andrewfernie/CADDeck/data/ButtonLayout10.png

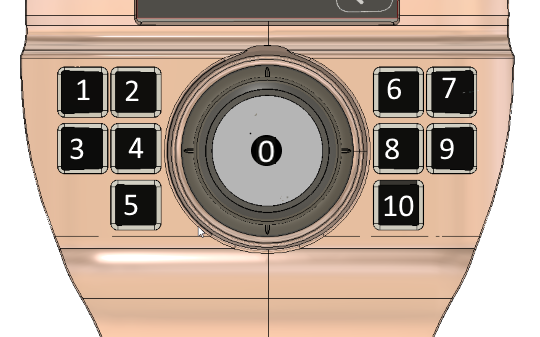
data/ButtonLayout10.png
