andrewfernie/CADDeck/data/ButtonLayout.png

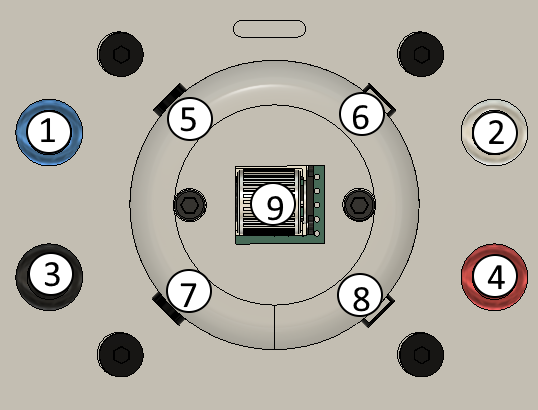
data/ButtonLayout.png
