andrewfernie/CADDeck/images/cadapp.png

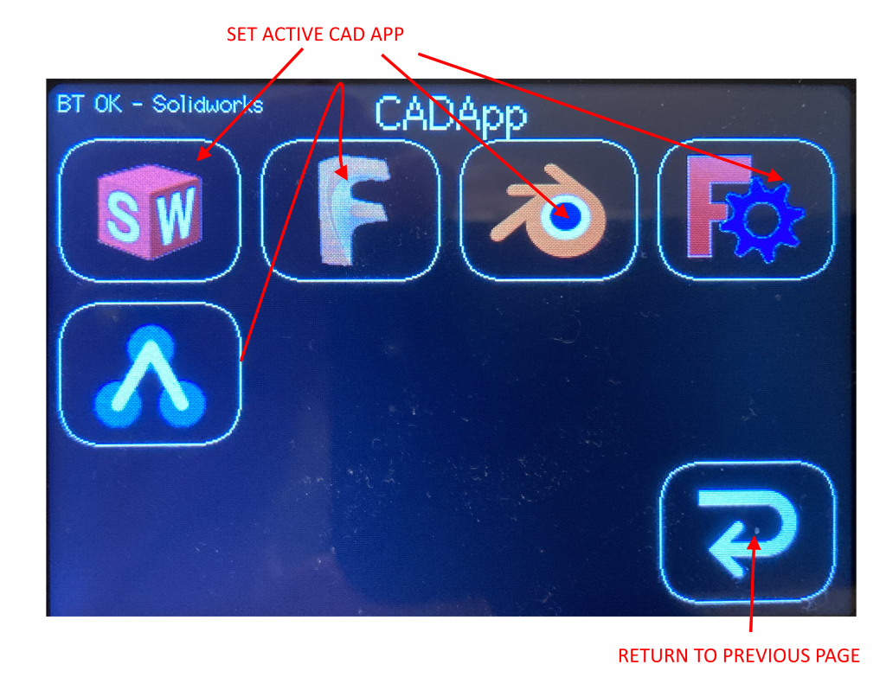
images/cadapp.png
