andrewfernie/CADDeck/images/Case.png

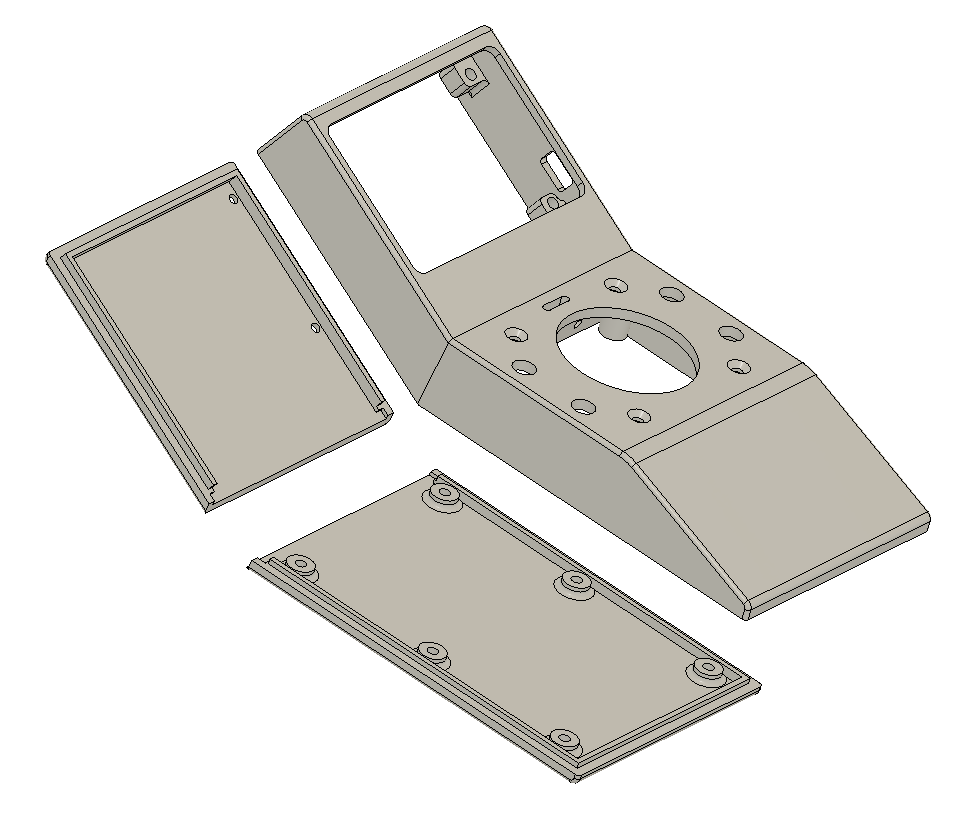
images/Case.png
