andrewfernie/CADDeck/images/ConfigurePan.png

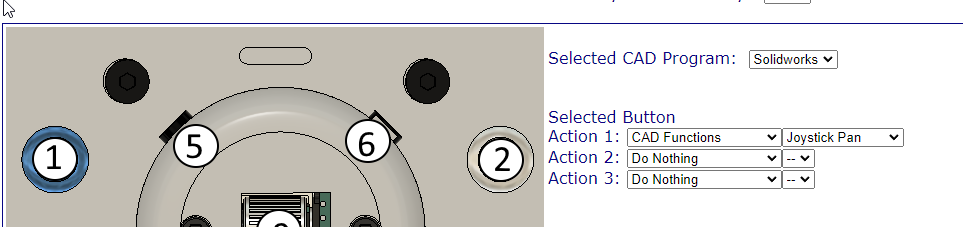
images/ConfigurePan.png
