andrewfernie/CADDeck/images/pcb.png

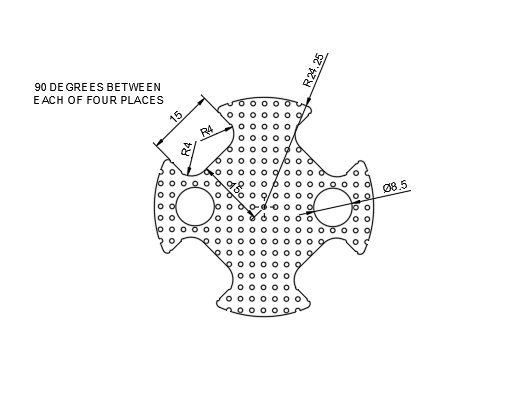
images/pcb.png
