andrewfernie/CADDeck/images/Assembly.png

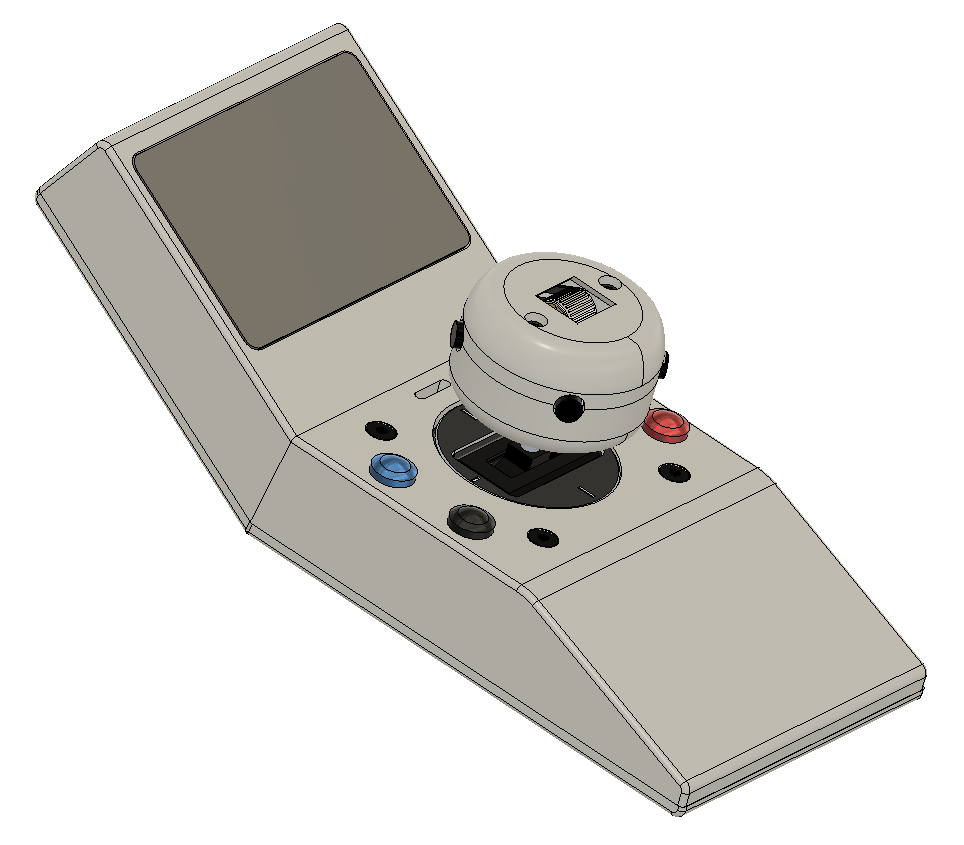
images/Assembly.png
