andrewfernie/CADDeck/hardware/Electrical/CADDeck.kicad_pcb

## KiCad design schematics/Microbee_Kit_Core_Board/rom_bank.kicad_sch

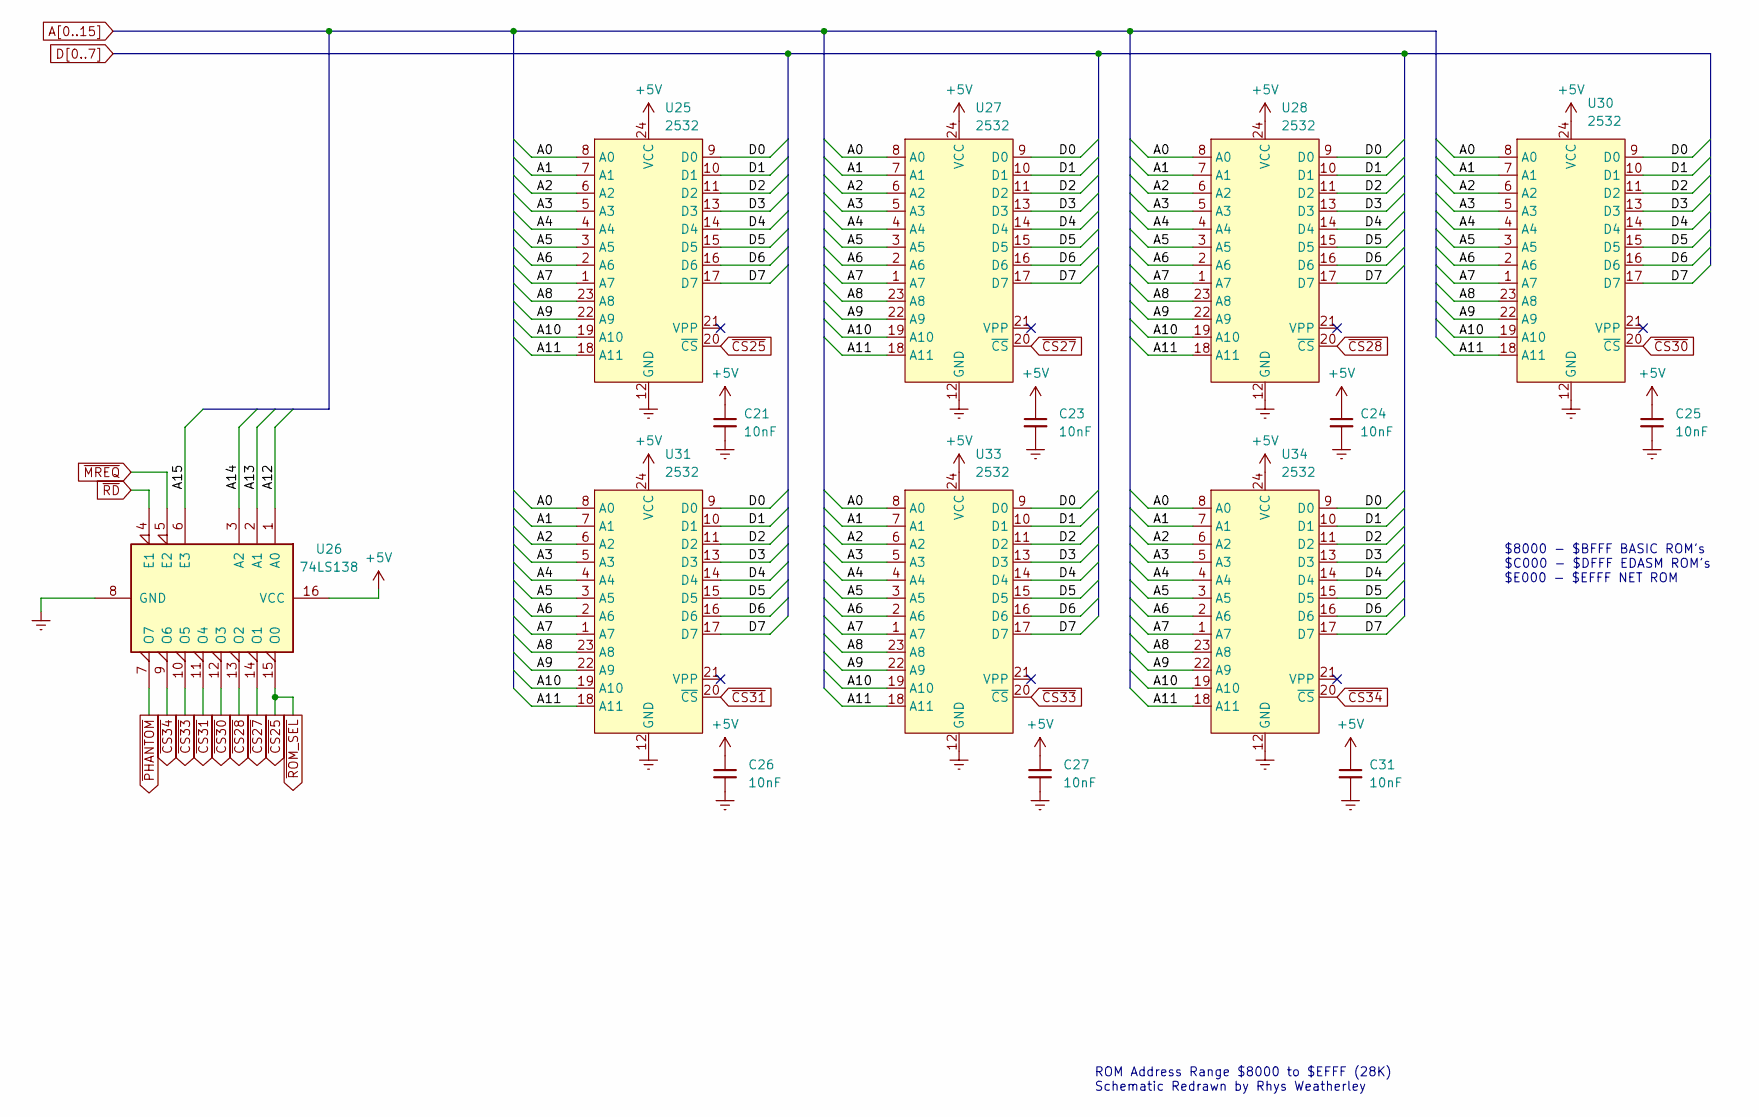
[picture p36: schematic rom_bank.kicad_sch]

Parts:
C21, C23, C24, C25, C26, C27, C31: 10nF
U25, U27, U28, U30, U31, U33, U34: 2532; DIP-24_W15.24mm
U26: 74LS138

Connections:
+5V: C21.1, C23.1, C24.1, C25.1, C26.1, C27.1, C31.1, U25.24 (VCC), U26.16 (VCC), U27.24 (VCC), U28.24 (VCC), U30.24 (VCC), U31.24 (VCC), U33.24 (VCC), U34.24 (VCC)
A0: U25.8 (A0), U27.8 (A0), U28.8 (A0), U30.8 (A0), U31.8 (A0), U33.8 (A0), U34.8 (A0)
A1: U25.7 (A1), U27.7 (A1), U28.7 (A1), U30.7 (A1), U31.7 (A1), U33.7 (A1), U34.7 (A1)
A2: U25.6 (A2), U27.6 (A2), U28.6 (A2), U30.6 (A2), U31.6 (A2), U33.6 (A2), U34.6 (A2)
A3: U25.5 (A3), U27.5 (A3), U28.5 (A3), U30.5 (A3), U31.5 (A3), U33.5 (A3), U34.5 (A3)
A4: U25.4 (A4), U27.4 (A4), U28.4 (A4), U30.4 (A4), U31.4 (A4), U33.4 (A4), U34.4 (A4)
A5: U25.3 (A5), U27.3 (A5), U28.3 (A5), U30.3 (A5), U31.3 (A5), U33.3 (A5), U34.3 (A5)
A6: U25.2 (A6), U27.2 (A6), U28.2 (A6), U30.2 (A6), U31.2 (A6), U33.2 (A6), U34.2 (A6)
A7: U25.1 (A7), U27.1 (A7), U28.1 (A7), U30.1 (A7), U31.1 (A7), U33.1 (A7), U34.1 (A7)
A8: U25.23 (A8), U27.23 (A8), U28.23 (A8), U30.23 (A8), U31.23 (A8), U33.23 (A8), U34.23 (A8)
A9: U25.22 (A9), U27.22 (A9), U28.22 (A9), U30.22 (A9), U31.22 (A9), U33.22 (A9), U34.22 (A9)
A10: U25.19 (A10), U27.19 (A10), U28.19 (A10), U30.19 (A10), U31.19 (A10), U33.19 (A10), U34.19 (A10)
A11: U25.18 (A11), U27.18 (A11), U28.18 (A11), U30.18 (A11), U31.18 (A11), U33.18 (A11), U34.18 (A11)
A12: U26.1 (A0)
A13: U26.2 (A1)
A14: U26.3 (A2)
A15: U26.6 (E3)
D0: U25.9 (D0), U27.9 (D0), U28.9 (D0), U30.9 (D0), U31.9 (D0), U33.9 (D0), U34.9 (D0)
D1: U25.10 (D1), U27.10 (D1), U28.10 (D1), U30.10 (D1), U31.10 (D1), U33.10 (D1), U34.10 (D1)
D2: U25.11 (D2), U27.11 (D2), U28.11 (D2), U30.11 (D2), U31.11 (D2), U33.11 (D2), U34.11 (D2)
D3: U25.13 (D3), U27.13 (D3), U28.13 (D3), U30.13 (D3), U31.13 (D3), U33.13 (D3), U34.13 (D3)
D4: U25.14 (D4), U27.14 (D4), U28.14 (D4), U30.14 (D4), U31.14 (D4), U33.14 (D4), U34.14 (D4)
D5: U25.15 (D5), U27.15 (D5), U28.15 (D5), U30.15 (D5), U31.15 (D5), U33.15 (D5), U34.15 (D5)
D6: U25.16 (D6), U27.16 (D6), U28.16 (D6), U30.16 (D6), U31.16 (D6), U33.16 (D6), U34.16 (D6)
D7: U25.17 (D7), U27.17 (D7), U28.17 (D7), U30.17 (D7), U31.17 (D7), U33.17 (D7), U34.17 (D7)
Earth: C21.2, C23.2, C24.2, C25.2, C26.2, C27.2, C31.2, U25.12 (GND), U26.8 (GND), U27.12 (GND), U28.12 (GND), U30.12 (GND), U31.12 (GND), U33.12 (GND), U34.12 (GND)
~CS25: U25.20 (~CS), U26.15 (O0)
~CS27: U26.14 (O1), U27.20 (~CS)
~CS28: U26.13 (O2), U28.20 (~CS)
~CS30: U26.12 (O3), U30.20 (~CS)
~CS31: U26.11 (O4), U31.20 (~CS)
~CS33: U26.10 (O5), U33.20 (~CS)
~CS34: U26.9 (O6), U34.20 (~CS)
~MREQ: U26.5 (E2)
~PHANTOM: U26.7 (O7)
~RD: U26.4 (E1)

Notes on the sheet:
$8000 - $BFFF BASIC ROM's $C000 - $DFFF EDASM ROM's $E000 - $EFFF NET ROM
ROM Address Range $8000 to $EFFF (28K) Schematic Redrawn by Rhys Weatherley
