andrewfernie/CADDeck/hardware/Electrical/CADDeck.kicad_pcb

## KiCad design schematics/Microbee_Kit_Main_Board/cpu_and_bus_tranceivers.kicad_sch

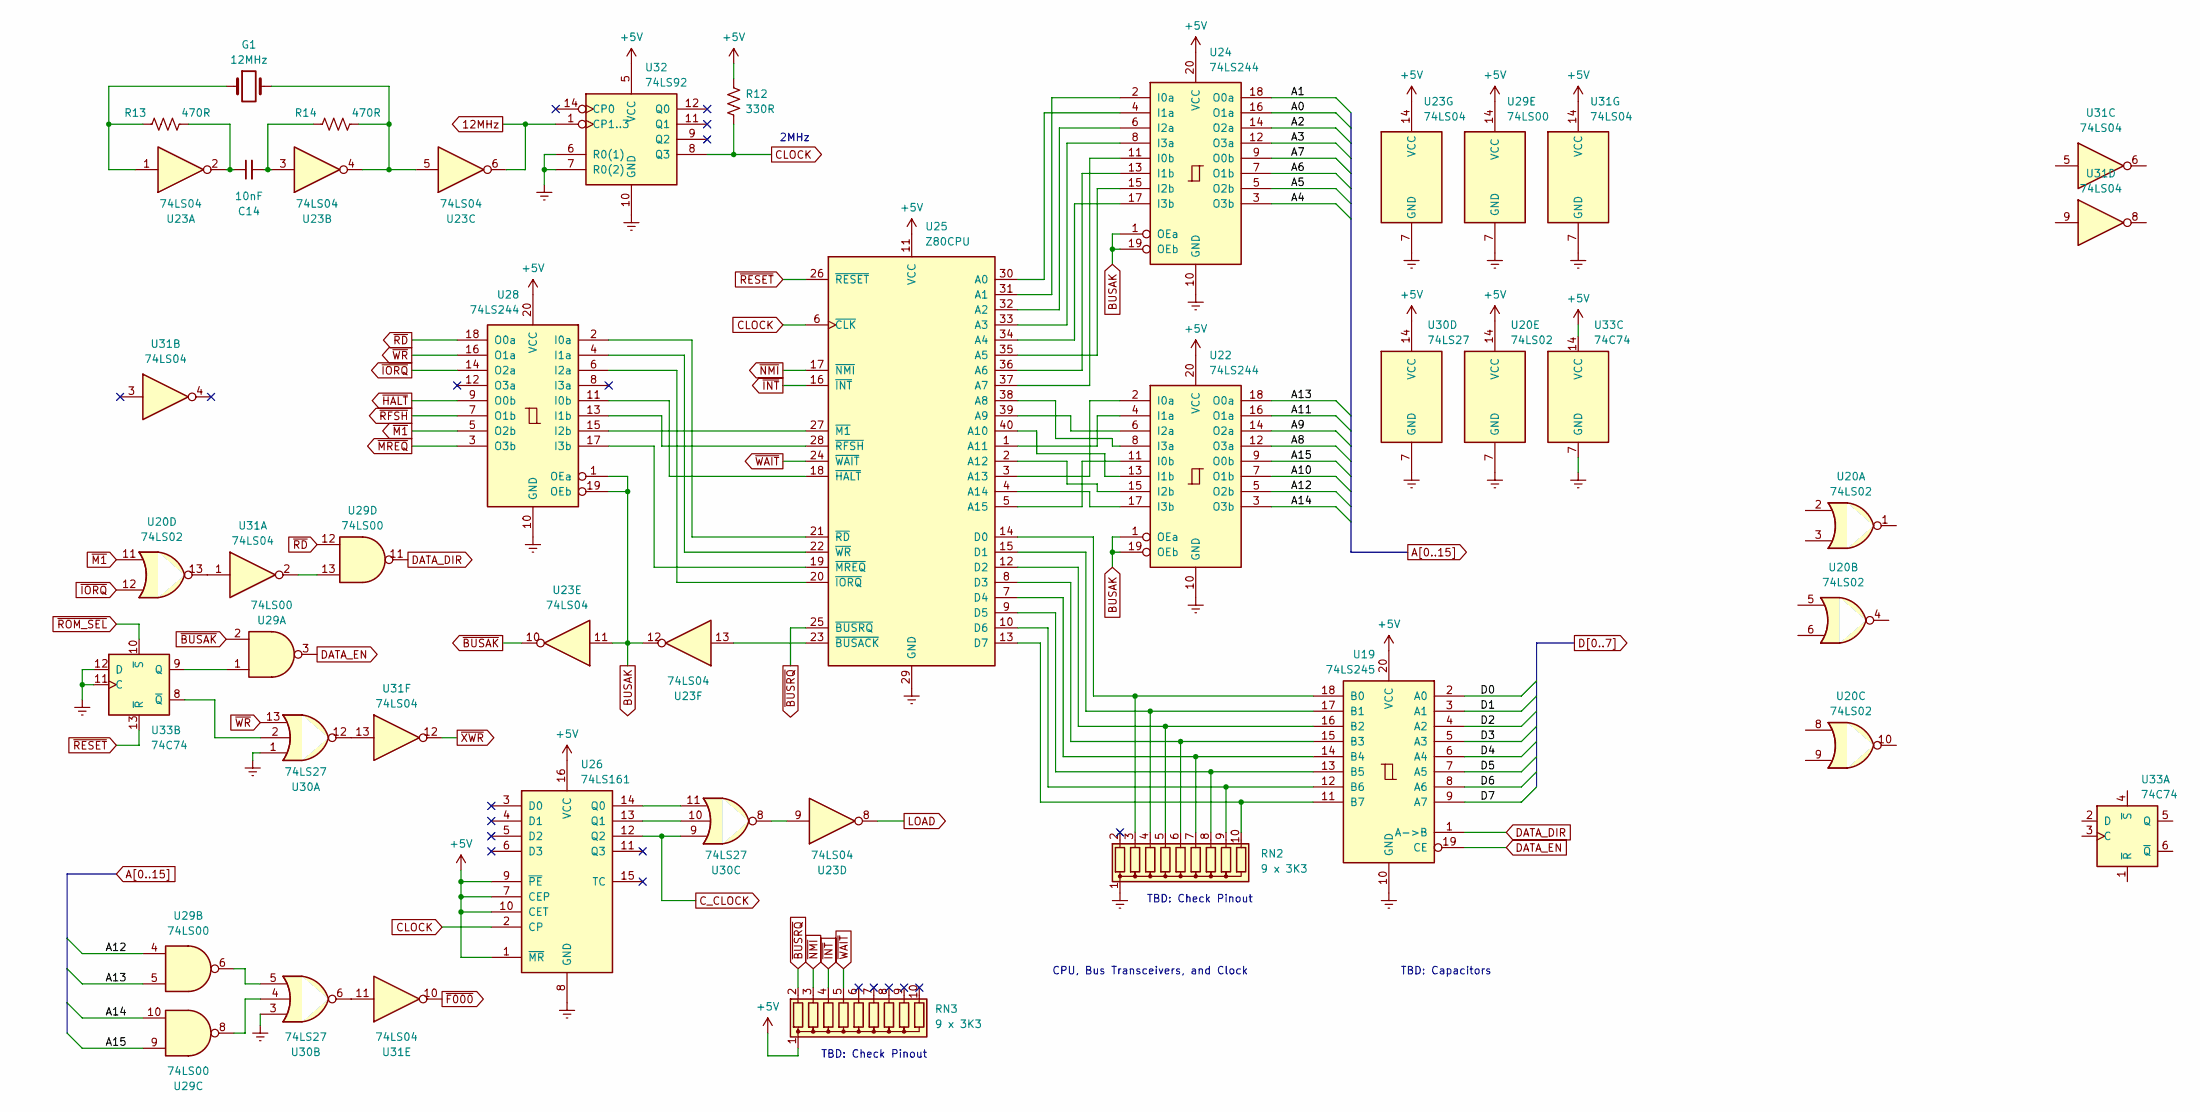
[picture p39: schematic cpu_and_bus_tranceivers.kicad_sch]

Parts:
C14: 10nF; C_Disc_D5.0mm_W2.5mm_P5.00mm
G1: 12MHz
R12: 330R; R_Axial_DIN0207_L6.3mm_D2.5mm_P7.62mm_Horizontal
R13, R14: 470R; R_Axial_DIN0207_L6.3mm_D2.5mm_P7.62mm_Horizontal
RN2, RN3: 9 x 3K3; R_Array_SIP10
U19: 74LS245; DIP-20_W7.62mm
U20: 74LS02
U22, U24, U28: 74LS244; DIP-20_W7.62mm
U23, U31: 74LS04
U25: Z80CPU; DIP-40_W15.24mm
U26: 74LS161; DIP-16_W7.62mm
U29: 74LS00
U30: 74LS27
U32: 74LS92; DIP-14_W7.62mm
U33: 74C74

Connections:
12MHz: U23.6, U32.1 (CP1..3)
+5V: R12.1, RN3.1 (common), U19.20 (VCC), U20.14 (VCC), U22.20 (VCC), U23.14 (VCC), U24.20 (VCC), U25.11 (VCC), U26.1 (~MR), U26.7 (CEP), U26.9 (~PE), U26.10 (CET), U26.16 (VCC), U28.20 (VCC), U29.14 (VCC), U30.14 (VCC), U31.14 (VCC), U32.5 (VCC), U33.14 (VCC)
A0: U24.16 (O1a)
A1: U24.18 (O0a)
A2: U24.14 (O2a)
A3: U24.12 (O3a)
A4: U24.3 (O3b)
A5: U24.5 (O2b)
A6: U24.7 (O1b)
A7: U24.9 (O0b)
A8: U22.12 (O3a)
A9: U22.14 (O2a)
A10: U22.7 (O1b)
A11: U22.16 (O1a)
A12: U22.5 (O2b), U29.4
A13: U22.18 (O0a), U29.5
A14: U22.3 (O3b), U29.10
A15: U22.9 (O0b), U29.9
BUSAK: U22.1 (OEa), U22.19 (OEb), U23.11, U23.12, U24.1 (OEa), U24.19 (OEb), U28.1 (OEa), U28.19 (OEb)
CLOCK: R12.2, U25.6 (~CLK), U26.2 (CP), U32.8 (Q3)
C_CLOCK: U26.12 (Q2), U30.9
D0: U19.2 (A0)
D1: U19.3 (A1)
D2: U19.4 (A2)
D3: U19.5 (A3)
D4: U19.6 (A4)
D5: U19.7 (A5)
D6: U19.8 (A6)
D7: U19.9 (A7)
DATA_DIR: U19.1 (A->B), U29.11
DATA_EN: U19.19 (CE), U29.3
Earth: RN2.1 (common), U19.10 (GND), U20.7 (GND), U22.10 (GND), U23.7 (GND), U24.10 (GND), U25.29 (GND), U26.8 (GND), U28.10 (GND), U29.7 (GND), U30.1, U30.3, U30.7 (GND), U31.7 (GND), U32.6 (R0(1)), U32.7 (R0(2)), U32.10 (GND), U33.7 (GND), U33.11 (C), U33.12 (D)
LOAD: U23.8
unnamed: C14.1, R13.2, U23.2
unnamed: C14.2, R14.1, U23.3
unnamed: G1.1, R13.1, U23.1
unnamed: G1.2, R14.2, U23.4, U23.5
unnamed: RN2.3 (R2), U19.18 (B0), U25.14 (D0)
unnamed: RN2.4 (R3), U19.17 (B1), U25.15 (D1)
unnamed: RN2.5 (R4), U19.16 (B2), U25.12 (D2)
unnamed: RN2.6 (R5), U19.15 (B3), U25.8 (D3)
unnamed: RN2.7 (R6), U19.14 (B4), U25.7 (D4)
unnamed: RN2.8 (R7), U19.13 (B5), U25.9 (D5)
unnamed: RN2.9 (R8), U19.12 (B6), U25.10 (D6)
unnamed: RN2.10 (R9), U19.11 (B7), U25.13 (D7)
unnamed: U20.13, U31.1
unnamed: U22.2 (I0a), U25.3 (A13)
unnamed: U22.4 (I1a), U25.1 (A11)
unnamed: U22.6 (I2a), U25.39 (A9)
unnamed: U22.8 (I3a), U25.38 (A8)
unnamed: U22.11 (I0b), U25.5 (A15)
unnamed: U22.13 (I1b), U25.40 (A10)
unnamed: U22.15 (I2b), U25.2 (A12)
unnamed: U22.17 (I3b), U25.4 (A14)
unnamed: U23.9, U30.8
unnamed: U23.13, U25.23 (~BUSACK)
unnamed: U24.2 (I0a), U25.31 (A1)
unnamed: U24.4 (I1a), U25.30 (A0)
unnamed: U24.6 (I2a), U25.32 (A2)
unnamed: U24.8 (I3a), U25.33 (A3)
unnamed: U24.11 (I0b), U25.37 (A7)
unnamed: U24.13 (I1b), U25.36 (A6)
unnamed: U24.15 (I2b), U25.35 (A5)
unnamed: U24.17 (I3b), U25.34 (A4)
unnamed: U25.18 (~HALT), U28.11 (I0b)
unnamed: U25.19 (~MREQ), U28.17 (I3b)
unnamed: U25.20 (~IORQ), U28.6 (I2a)
unnamed: U25.21 (~RD), U28.2 (I0a)
unnamed: U25.22 (~WR), U28.4 (I1a)
unnamed: U25.27 (~M1), U28.15 (I2b)
unnamed: U25.28 (~RFSH), U28.13 (I1b)
unnamed: U26.13 (Q1), U30.10
unnamed: U26.14 (Q0), U30.11
unnamed: U29.1, U33.9 (Q)
unnamed: U29.6, U30.5
unnamed: U29.8, U30.4
unnamed: U29.13, U31.2
unnamed: U30.2, U33.8 (~Q)
unnamed: U30.6, U31.11
unnamed: U30.12, U31.13
~BUSAK: U23.10, U29.2
~BUSRQ: RN3.2 (R1), U25.25 (~BUSRQ)
~F000: U31.10
~HALT: U28.9 (O0b)
~INT: RN3.4 (R3), U25.16 (~INT)
~IORQ: U20.12, U28.14 (O2a)
~M1: U20.11, U28.5 (O2b)
~MREQ: U28.3 (O3b)
~NMI: RN3.3 (R2), U25.17 (~NMI)
~RD: U28.18 (O0a), U29.12
~RESET: U25.26 (~RESET), U33.13 (~R)
~RFSH: U28.7 (O1b)
~ROM_SEL: U33.10 (~S)
~WAIT: RN3.5 (R4), U25.24 (~WAIT)
~WR: U28.16 (O1a), U30.13
~XWR: U31.12

Notes on the sheet:
CPU, Bus Transceivers, and Clock
2MHz
TBD: Capacitors
TBD: Check Pinout
