andrewfernie/CADDeck/hardware/Electrical/CADDeck.kicad_pcb

## KiCad design schematics/Microbee_Kit_Main_Board/cpu_and_io.kicad_sch

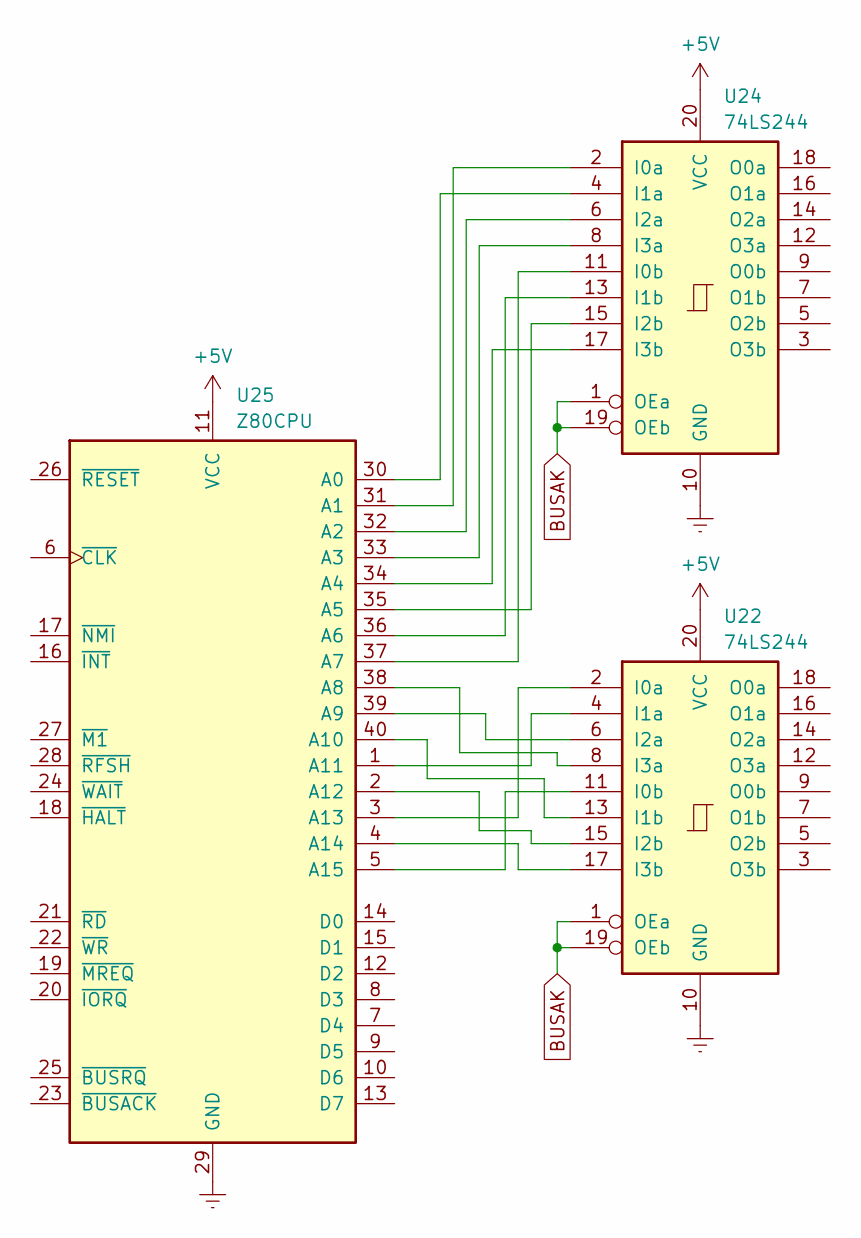
[picture p40: schematic cpu_and_io.kicad_sch]

Parts:
U22, U24: 74LS244
U25: Z80CPU

Connections:
+5V: U22.20 (VCC), U24.20 (VCC), U25.11 (VCC)
BUSAK: U22.1 (OEa), U22.19 (OEb), U24.1 (OEa), U24.19 (OEb)
Earth: U22.10 (GND), U24.10 (GND), U25.29 (GND)
unnamed: U22.2 (I0a), U25.3 (A13)
unnamed: U22.4 (I1a), U25.1 (A11)
unnamed: U22.6 (I2a), U25.39 (A9)
unnamed: U22.8 (I3a), U25.38 (A8)
unnamed: U22.11 (I0b), U25.5 (A15)
unnamed: U22.13 (I1b), U25.40 (A10)
unnamed: U22.15 (I2b), U25.2 (A12)
unnamed: U22.17 (I3b), U25.4 (A14)
unnamed: U24.2 (I0a), U25.31 (A1)
unnamed: U24.4 (I1a), U25.30 (A0)
unnamed: U24.6 (I2a), U25.32 (A2)
unnamed: U24.8 (I3a), U25.33 (A3)
unnamed: U24.11 (I0b), U25.37 (A7)
unnamed: U24.13 (I1b), U25.36 (A6)
unnamed: U24.15 (I2b), U25.35 (A5)
unnamed: U24.17 (I3b), U25.34 (A4)
