andrewfernie/CADDeck/hardware/Electrical/CADDeck.kicad_pcb

## KiCad design schematics/Microbee_Kit_Main_Board/video_memory.kicad_sch

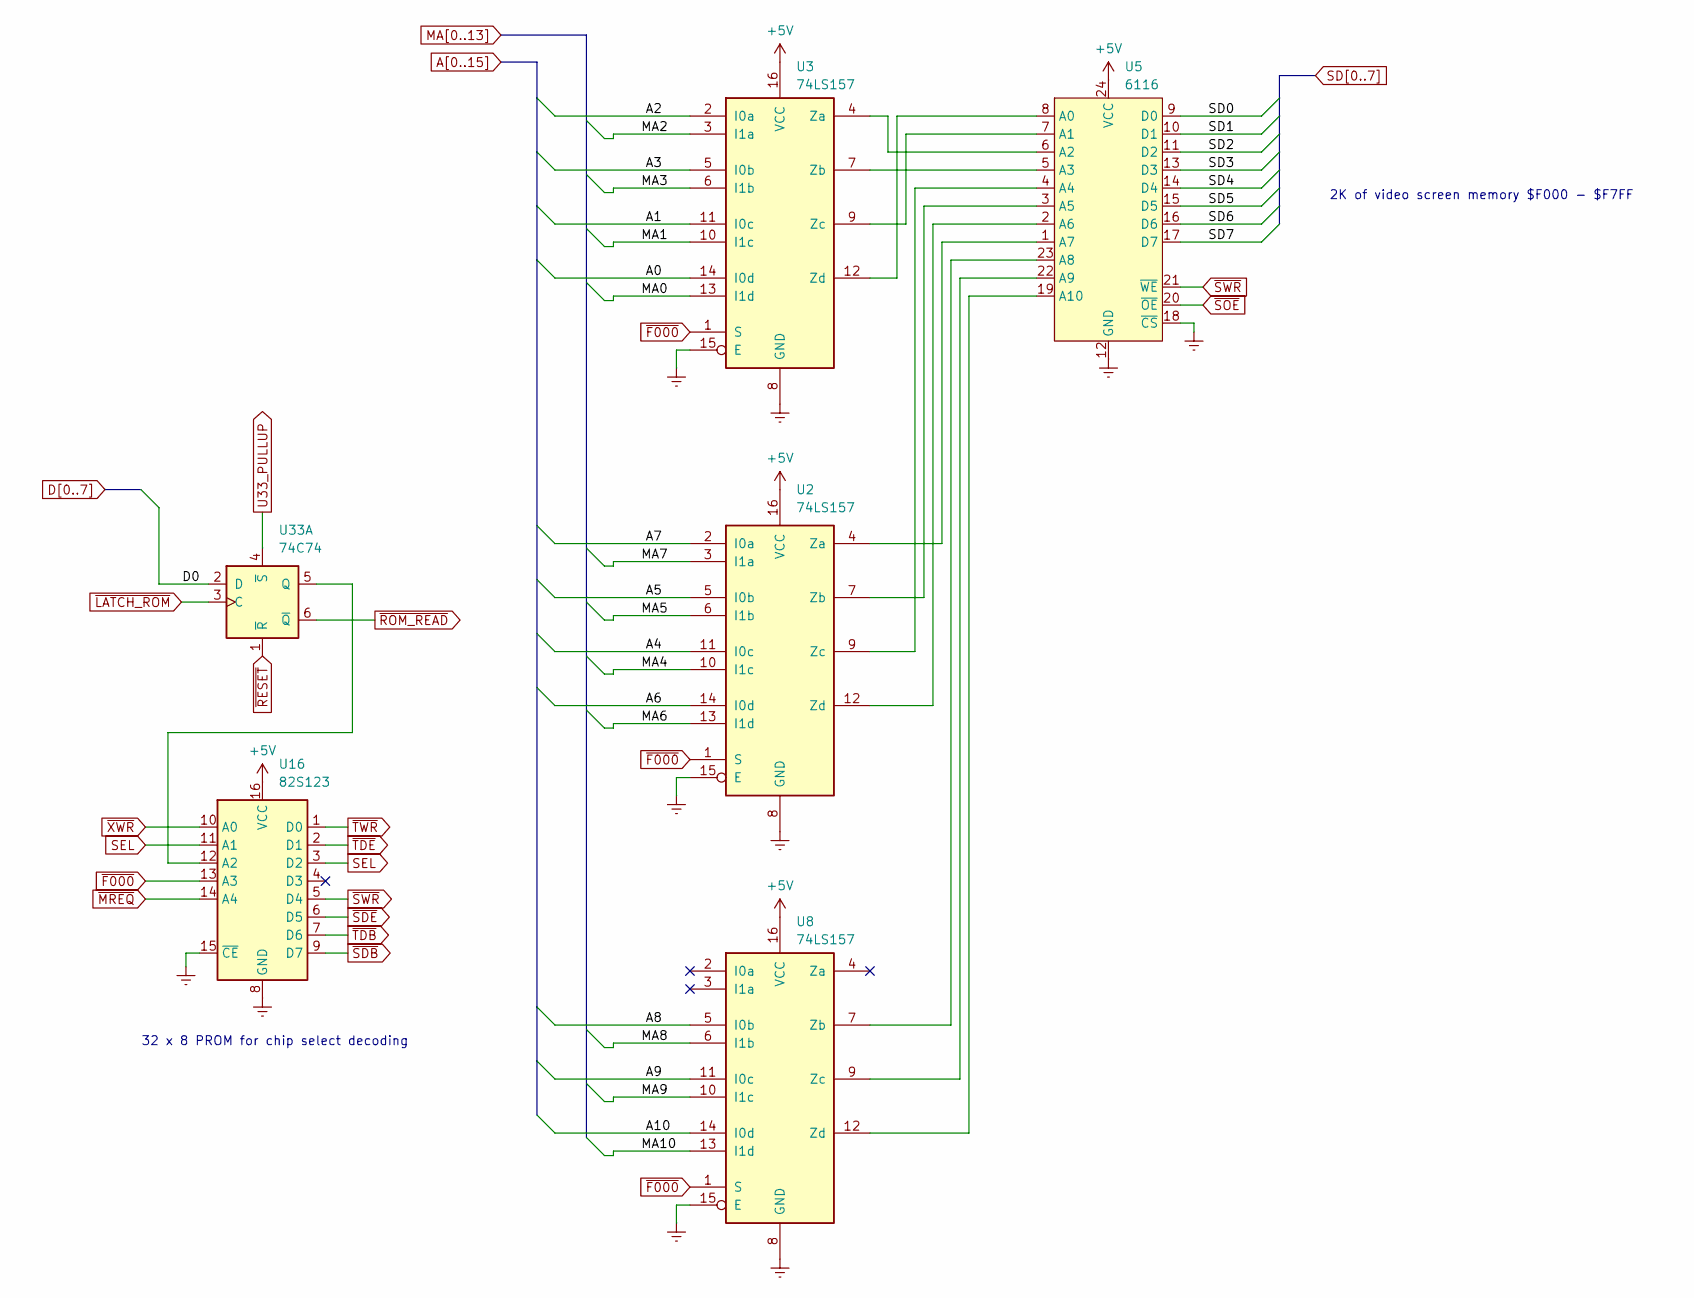
[picture p44: schematic video_memory.kicad_sch]

Parts:
U2, U3, U8: 74LS157; DIP-16_W7.62mm
U5: 6116; DIP-24_W15.24mm
U16: 82S123
U33: 74C74; DIP-14_W7.62mm

Connections:
+5V: U2.16 (VCC), U3.16 (VCC), U5.24 (VCC), U8.16 (VCC), U16.16 (VCC)
A0: U3.14 (I0d)
A1: U3.11 (I0c)
A2: U3.2 (I0a)
A3: U3.5 (I0b)
A4: U2.11 (I0c)
A5: U2.5 (I0b)
A6: U2.14 (I0d)
A7: U2.2 (I0a)
A8: U8.5 (I0b)
A9: U8.11 (I0c)
A10: U8.14 (I0d)
D0: U33.2 (D)
Earth: U2.8 (GND), U2.15 (E), U3.8 (GND), U3.15 (E), U5.12 (GND), U5.18 (~CS), U8.8 (GND), U8.15 (E), U16.8 (GND), U16.15 (~CE)
MA0: U3.13 (I1d)
MA1: U3.10 (I1c)
MA2: U3.3 (I1a)
MA3: U3.6 (I1b)
MA4: U2.10 (I1c)
MA5: U2.6 (I1b)
MA6: U2.13 (I1d)
MA7: U2.3 (I1a)
MA8: U8.6 (I1b)
MA9: U8.10 (I1c)
MA10: U8.13 (I1d)
unnamed: U2.4 (Za), U5.1 (A7)
unnamed: U2.7 (Zb), U5.3 (A5)
unnamed: U2.9 (Zc), U5.4 (A4)
unnamed: U2.12 (Zd), U5.2 (A6)
unnamed: U3.4 (Za), U5.6 (A2)
unnamed: U3.7 (Zb), U5.5 (A3)
unnamed: U3.9 (Zc), U5.7 (A1)
unnamed: U3.12 (Zd), U5.8 (A0)
unnamed: U5.19 (A10), U8.12 (Zd)
unnamed: U5.22 (A9), U8.9 (Zc)
unnamed: U5.23 (A8), U8.7 (Zb)
unnamed: U16.12 (A2), U33.5 (Q)
SD0: U5.9 (D0)
SD1: U5.10 (D1)
SD2: U5.11 (D2)
SD3: U5.13 (D3)
SD4: U5.14 (D4)
SD5: U5.15 (D5)
SD6: U5.16 (D6)
SD7: U5.17 (D7)
SEL: U16.3 (D2), U16.11 (A1)
U33_PULLUP: U33.4 (~S)
~F000: U2.1 (S), U3.1 (S), U8.1 (S), U16.13 (A3)
~LATCH_ROM: U33.3 (C)
~MREQ: U16.14 (A4)
~RESET: U33.1 (~R)
~ROM_READ: U33.6 (~Q)
~SDB: U16.9 (D7)
~SDE: U16.6 (D5)
~SOE: U5.20 (~OE)
~SWR: U5.21 (~WE), U16.5 (D4)
~TDB: U16.7 (D6)
~TDE: U16.2 (D1)
~TWR: U16.1 (D0)
~XWR: U16.10 (A0)

Notes on the sheet:
2K of video screen memory $F000 - $F7FF
32 x 8 PROM for chip select decoding
