andrewfernie/CADDeck/include/CADDeck.h

#pragma once

#define BLUETOOTH_COMMANDS   // Enable Bluetooth commands (BLE Keyboard and BLE Mouse). Otherwise only USB commands are enabled. (IN WORK)

// Select UI language
#define LANGUAGE_ENGLISH
// #define LANGUAGE_GERMAN

// Basic macros for debug and info messages to the serial port
// If too many messages are being sent the web server used for the configurator may not work as well. 
#define LOG_MSG_BASIC 1
#define LOG_MSG_LEVEL 2  // 1=ERROR, 2=ERROR+WARN, 3=ERROR+WARN+INFO
#define LOG_MSG_DEBUG 1
#define LOG_MSG_TOUCH_DEBUG 0 // messages to console each time a touch is detected
#define LOG_MSG_JOYSTICK_MODE 0  // messages to console for joystick mode debug

//#define LOG_JSON_FILES  // log the contents of the JSON files to the console. Comment out to disable.

#include "std_defs.h"

// NOTE: The hardware configuration for the display (pins, display type, etc.) is defined in the platformio.ini file.
// This avoids the need to modify files in the TFT_eSPI library, which would be overwritten when the library is updated.

#ifdef BLUETOOTH_COMMANDS
#include <BleCombo.h>     // BLE combo library (Keyboard and Mouse)
#else
#endif
#include <FS.h>           // Filesystem support header
#include <Preferences.h>  // Used to store states before sleep/reboot
#include <TFT_eSPI.h>     // The TFT_eSPI library
#include <pgmspace.h>     // PROGMEM support header

// Define the storage to be used.
#define FILESYSTEM_LITTLEFS

#ifdef FILESYSTEM_LITTLEFS
#define FILESYSTEM LittleFS
#include <LittleFS.h>  // https://github.com/lorol/LITTLEFS
#else
#define FILESYSTEM SPIFFS
#include <SPIFFS.h>  // Filesystem support header
#endif

#ifdef BLUETOOTH_COMMANDS
#if defined(USE_NIMBLE)

#include "NimBLEBeacon.h"  // Additional BLE functionaity using NimBLE
#include "NimBLEDevice.h"  // Additional BLE functionaity using NimBLE
#include "NimBLEUtils.h"   // Additional BLE functionaity using NimBLE

#else

#include "BLEBeacon.h"  // Additional BLE functionaity
#include "BLEDevice.h"  // Additional BLE functionaity
#include "BLEUtils.h"   // Additional BLE functionaity

#endif  // USE_NIMBLE
#endif

#include <ArduinoJson.h>        // Using ArduinoJson to read and write config files
#include <AsyncTCP.h>           //Async Webserver support header
#include <ESPAsyncWebServer.h>  //Async Webserver support header
#include <ESPmDNS.h>            // DNS functionality
#include <WiFi.h>               // Wifi support

#ifdef BLUETOOTH_COMMANDS
#include "esp_bt_device.h"  // Additional BLE functionaity
#include "esp_bt_main.h"    // Additional BLE functionaity
#endif
#include "esp_sleep.h"      // Additional BLE functionaity

#include "DrawHelper.h"
#include "Action.h"
#include "ConfigHelper.h"
#include "ConfigLoad.h"
#include "ScreenHelper.h"
#include "Touch.h"
#include "UserActions.h"
#include "Webserver.h"
#include "Physical_IO.h"
#include "SerialCommands.h"
#include "stack_queue.h"
#include "SpaceMouse.h"

#define MIN_TO_MS 60 * 1000

const long loop_period = 20;  // 20ms loop period

const uint8_t LEN_FILENAME = 32;    // length of filenames (e.g. for logos, menus, etc). Includes the file extension
const uint8_t LEN_DESCRIPTION = 32; // length of h/W and menu button descriptions
const uint8_t LEN_NAME = 32;        // length of menu name

// ------- Uncomment the define below if you want to use a piezo buzzer and specify the pin where the speaker is connected -------
// #define speakerPin 26

// ------- Enable to read and report battery voltage.  -------
//#define READ_EXTERNAL_BATTERY
#ifdef READ_EXTERNAL_BATTERY
#define EXTERNAL_BATTERY_PIN 33
#define EXTERNAL_BATTERY_ADC_SCALE (3.3 / 4095.0)                   // Default attenuation results in 2.6V for full scale on ADC
#define EXTERNAL_BATTERY_SCALE (EXTERNAL_BATTERY_ADC_SCALE * 2.13)  // include any input voltage dividers here
#endif

// ------- NimBLE definition, use only if the NimBLE library is installed
// and if you are using the original ESP32-BLE-Keyboard library by T-VK -------
// #define USE_NIMBLE

// CADDeck version number
extern const char* versionnumber;

// ------- Uncomment the define below if you want to preload the logos to PSRAM at start (adds about 10s to startup) -------
// #define PRELOAD_LOGOS

// Logo Size
#define LOGO_SIZE_X_Y 75

// Button layout and number of pages with buttons
#define BUTTON_ROWS 3
#define BUTTON_COLS 4
#define BUTTONS_PER_PAGE (BUTTON_ROWS * BUTTON_COLS)
#define NUM_PAGES 10  // Includes Menu0 which is the home page

// Gaps between buttons
// First - strictly define the gap between each button
#define KEY_SPACING_X 12
#define KEY_SPACING_Y 12

// Define or calculate a margin around the edge of the display (default is half of the key spacing value)
// Separate values for top and bottom allow for a status bar at the top or bottom of the screen
#define STATUS_BAR_HEIGHT_TOP 26
#define STATUS_BAR_HEIGHT_BOTTOM 0
#define KEY_MARGIN_X (KEY_SPACING_X / 2)
#define KEY_MARGIN_Y_TOP (STATUS_BAR_HEIGHT_TOP + KEY_SPACING_Y / 2)
#define KEY_MARGIN_Y_BOTTOM (STATUS_BAR_HEIGHT_BOTTOM + KEY_SPACING_Y / 2)

// Width and height of a button
// Second - define button width based on spacing and number of buttons (use what's left)
#define KEY_W ((SCREEN_WIDTH - (2 * KEY_MARGIN_X)) - (BUTTON_COLS - 1) * (KEY_SPACING_X + 1)) / BUTTON_COLS
#define KEY_H ((SCREEN_HEIGHT - (KEY_MARGIN_Y_TOP + KEY_MARGIN_Y_BOTTOM)) - (BUTTON_ROWS - 1) * (KEY_SPACING_Y + 1)) / BUTTON_ROWS

// Keypad start position, centre of the first button
#define KEY_X KEY_MARGIN_X + (KEY_W / 2)
#define KEY_Y KEY_MARGIN_Y_TOP + (KEY_H / 2)

// Font size multiplier
#define KEY_TEXTSIZE 1

// Display of wifi password when wifi is enabled
// #define WIFI_PASSWORD_DISPLAY

// Touch panel definition
#ifdef USECAPTOUCH
// ------- Uncomment and populate the following if your cap touch uses custom i2c pins -------
#define CUSTOM_TOUCH_SDA PIN_SDA
#define CUSTOM_TOUCH_SCL PIN_SCL

// With a capacitive touch screen the choice is between the FT6336U library and the FT6236 library from Dustin Watts
// The FT6336U library supports multi-touch, which is not used yet in this project, but might be in the future.
// At present, either will work fine.
#define USE_FT6336U_LIB
#include <Wire.h>
#ifdef USE_FT6336U_LIB
#include "FT6336U.h"
extern FT6336U ts;
#else
#include "FT6236.h"
extern FT6236 ts;
#endif
#else
#include "Touch.h"
#endif

// extern BleKeyboard bleKeyboard;

extern AsyncWebServer webserver;

extern TFT_eSPI tft;

extern Preferences savedStates;

extern bool psramAvailable;

// ---------------- SpaceMouse Support ----------------
// enable support for SpaceMouse emulation on Serial 1
#define SPACEMOUSE_SUPPORT  // Comment out to disable SpaceMouse support
#define SPACEMOUSE_RX_PIN 5
#define SPACEMOUSE_TX_PIN 4
#define SPACEMOUSE_BAUD 115200
#define SPACEMOUSE_CONFIG SERIAL_8N1
#define SPACEMOUSE_SERIAL Serial1
extern SpaceMouse spaceMouse;

// ---------------- Debug pins ----------------
// set to 1 to enable debug pins, 0 to disable
#define USE_DEBUG_PINS 0

// Careful with which pins you use - they may be used for other functions
const uint8_t DEBUG_PIN_1 = 25;
const uint8_t DEBUG_PIN_2 = 26;
const uint8_t DEBUG_PIN_3 = 27;
const uint8_t DEBUG_PIN_4 = 5;

// ---------------- Touch Screen Calibration ----------------
// Applies only to resistive touch screens.
// This is the file name used to store the calibration data
// You can change this to create new calibration files.
// The FILESYSTEM file name must start with "/".
#define CALIBRATION_FILE "/TouchCalData"

// Set REPEAT_CAL to true instead of false to run calibration
// again, otherwise it will only be done once.
// Repeat calibration if you change the screen rotation.
#define REPEAT_CAL false

// Text Button Label Font
#define LABEL_FONT &FreeSansBold12pt7b

// placeholder for the pagenumber we are on (0 indicates home)
extern int pageNum;
extern Stack pageHistoryStack;

// Initial LED brightness
extern int ledBrightness;

// path to the directory the logo are in ! including leading AND trailing / !
extern char logopath[64];

// templogopath is used to hold the complete path of an image. It is empty for now.
extern char templogopath[64];

extern uint8_t last_hwbutton_state[];

extern long loop_count;

// Struct Action: actions and value
struct Actions {
    uint8_t action;
    uint8_t value;
    char symbol[64];
};

// Each button has an action struct in it
struct Button {
    Actions actions[3];
    bool latch;
    bool islatched;
    char logo[LEN_FILENAME];
    char latchlogo[LEN_FILENAME];
    char description[LEN_DESCRIPTION];
    uint16_t imageBGColour;
    uint16_t latchImageBGColour;
    uint8_t imageBGColourValid;
    uint8_t latchImageBGColourValid;
    uint16_t* pImage;
    uint16_t* pLatchImage;
};

// Each menu has an array of buttons

struct MenuLayout {
    uint16_t logo_size_x_y;
    uint16_t button_rows;
    uint16_t button_cols;
    uint16_t button_size_x_y;
    uint16_t key_spacing_x;
    uint16_t key_spacing_y;
    uint16_t status_bar_height_top;
    uint16_t status_bar_height_bottom;
};

struct Menu {
    char name[LEN_NAME];
    MenuLayout layout;
    Button button[BUTTON_ROWS][BUTTON_COLS];
};

// Struct to hold the general logos.
struct Generallogos {
    char homebutton[64];
    char configurator[64];
};

// Struct to hold the general config like colours.
struct Config {
    uint16_t menuButtonColour;
    uint16_t functionButtonColour;
    uint16_t backgroundColour;
    uint16_t latchedColour;
    bool sleepenable;
    uint16_t sleeptimer;
    bool usbcommsenable;
    bool beep; 
    uint8_t modifier1;
    uint8_t modifier2;
    uint8_t modifier3;
    uint16_t helperdelay;
    uint16_t startup_menu;
    uint8_t gpio_pin;
    uint8_t gpio_pin_mode;
};

const uint8_t CADCONFIG_VERSION = 2;
struct CADConfig {
    uint8_t version;
    uint8_t current_program;
    float joy_scale_x;
    float joy_scale_y;
    float joy_deadzone;
    float joy_sensitivity;
    float zoom_scale;
    float zoom_deadzone;
    float zoom_sensitivity;
    float rotate_scale;
    float rotate_deadzone;
    float rotate_sensitivity;
    float mouse_sensitivity;
    uint16_t num_programs;
    bool spacemouse_enable;
};

#define NUM_HW_BUTTONS 11
struct CADProgramConfig {
    uint8_t version;
    char name[LEN_NAME];
    char logo[LEN_FILENAME];
    uint8_t default_joystick_mode;
    Actions pan[3];
    Actions tilt[3];
    Actions zoom[3];
    Actions rotate[3];
    uint16_t num_buttons;
    char hw_button_descriptions[NUM_HW_BUTTONS][LEN_DESCRIPTION];
    Actions hw_buttons[NUM_HW_BUTTONS][3];
    uint8_t hw_button_state[NUM_HW_BUTTONS];
};

struct Wificonfig {
    char ssid[64];
    char password[64];
    char wifimode[9];
    char hostname[64];
    uint8_t attempts;
    uint16_t attemptdelay;
};

// Create instances of the structs
extern Wificonfig wificonfig;

extern Config generalconfig;

extern CADConfig cadconfig;

#define NUM_CAD_PROGRAMS 5
extern CADProgramConfig cadprogramconfig[];

// And finally, we have an array of menus
extern Menu menu[NUM_PAGES];

extern Generallogos generallogo;



// struct Logos screen[NUM_PAGES];

extern unsigned long previousMillis;
extern unsigned long Interval;
extern bool displayinginfo;
extern bool displayingIOValues;
extern bool displayingButtonDescriptions;
extern char jsonFileFail[32];

// Invoke the TFT_eSPI button class and create all the button objects
extern TFT_eSPI_Button key[BUTTON_ROWS][BUTTON_COLS];

#ifdef BLUETOOTH_COMMUNICATION
// Checking for BLE Keyboard version
#ifndef BLE_COMBO_VERSION
#warning Original ESP32-BLE-Combo Keyboard version detected. Please check.
#define BLE_COMBO_VERSION "Outdated"
#endif
#endif

// Special pages
#define WEB_REQUEST_PAGE (NUM_PAGES + 1)
#define SPECIAL_PAGE_INFO (NUM_PAGES + 2)
#define SPECIAL_3_PAGE (NUM_PAGES + 3)
#define SPECIAL_4_PAGE (NUM_PAGES + 4)
#define SPECIAL_PAGE_IO_MONITOR (NUM_PAGES + 5)
#define SPECIAL_PAGE_BUTTON_INFO (NUM_PAGES + 6)
#define MAX_PAGE_NUM (NUM_PAGES + 6)  // update this to the highest special page number

//--------- Internal references ------------
// (this needs to be below all structs etc..)
enum ActionEnum
{
    Action_NoAction = 0,
    Action_Delay = 1,
    Action_TabArrow = 2,
    Action_Media = 3,
    Action_Char = 4,
    Action_Option = 5,
    Action_FnKey = 6,
    Action_Number = 7,
    Action_SpecialChar = 8,
    Action_Combos = 9,
    Action_Helpers = 10,
    Action_SpecialFn = 11,
    Action_Numpad = 12,
    Action_CustomFn = 13,
    Action_ChangePage = 14,
    Action_CADFn = 15,
    Action_CADProgram = 16,
    Action_MouseButton = 17,
    Action_PreviousPage = 18,
    Action_DefaultJoyMode = 19,
    Action_SpaceMouseButton = 20
};

enum CADFnEnum {
    CADFn_NoAction = 0,
    CADFn_SetCADProgram = 1,
    CADFn_CalibrateZero = 2,
    CADFn_CalibrateControlScale = 3,
    CADFn_Spare1 = 4,
    CADFn_Spare2 = 5,
    CADFn_InvertJoyScaleX = 6,
    CADFn_InvertJoyScaleY = 7,
    CADFn_InvertScaleZoom = 8,
    CADFn_InvertScaleRotate = 9,
    CADFn_SaveCADConfig = 10,
    CADFn_Spare3 = 11,
    CADFn_Spare4 = 12,
    CADFn_Spare5 = 13,
    CADFn_Spare6 = 14,
    CADFn_ModeSelect = 15
};

enum JoystickMode {
    JoystickModeNone = 0,
    JoystickModePan = 1,
    JoystickModeTilt = 2,
    JoystickModeZoom = 3,
    JoystickModeRotate = 4,
    JoystickModeMouse = 5
};

enum CADApplications {
    CADApp_SolidWorks = 0,
    CADApp_Fusion360 = 1,
    CADApp_Blender = 2,
    CADApp_FreeCAD = 3,
    CADApp_AC3D = 4
};

enum SpecialFn
{
    SpecialFn_NoAction = 0,
    SpecialFn_ConfigMode = 1,
    SpecialFn_DisplayBrightnessDown = 2,
    SpecialFn_DisplayBrightnessUp = 3,
    SpecialFn_SleepEnable = 4,
    SpecialFn_InfoPage = 5,
    SpecialFn_HomePage = 6,
    SpecialFn_SaveConfig = 7,
    SpecialFn_USBComm = 8,
    SpecialFn_IOMonitor = 9,
    SpecialFn_GPIO_Toggle = 10,
    SpecialFn_GPIO_Off = 11,
    SpecialFn_GPIO_On = 12,
    SpecialFn_ButtonInfoPage = 13,
    SpecialFn_Spacemouse_Enable_Toggle = 14
};

enum MouseButton {
    MouseButton_PL = 1,
    MouseButton_PR = 2,
    MouseButton_PM = 3,
    MouseButton_PLM = 4, 
    MouseButton_PRM = 5,
    MouseButton_RL = 6,
    MouseButton_RR = 7,
    MouseButton_RM = 8,
    MouseButton_RLM = 9,
    MouseButton_RRM = 10,
    MouseButton_RLRM = 11
};

enum OptionKeys {
    OptionKey_LCtrl = 1,
    OptionKey_LShift = 2,
    OptionKey_LAlt = 3,
    OptionKey_LGui = 4,
    OptionKey_RCtrl = 5,
    OptionKey_RShift = 6,
    OptionKey_RAlt = 7,
    OptionKey_RGui = 8,
    OptionKey_ReleaseAll = 9
};

enum ActionNumpadKeys {
    ActionNumpadKey_0 = 0,
    ActionNumpadKey_1 = 1,
    ActionNumpadKey_2 = 2,
    ActionNumpadKey_3 = 3,
    ActionNumpadKey_4 = 4,
    ActionNumpadKey_5 = 5,
    ActionNumpadKey_6 = 6,
    ActionNumpadKey_7 = 7,
    ActionNumpadKey_8 = 8,
    ActionNumpadKey_9 = 9,
    ActionNumpadKey_Slash = 10,
    ActionNumpadKey_Asterix = 11,
    ActionNumpadKey_Minus = 12,
    ActionNumpadKey_Plus = 13,
    ActionNumpadKey_Enter = 14,
    ActionNumpadKey_Period = 15
};

enum ActionCustomFnKeys
{
    ActionCustomFnKey_1 = 1,
    ActionCustomFnKey_2 = 2,
    ActionCustomFnKey_3 = 3,
    ActionCustomFnKey_4 = 4,
    ActionCustomFnKey_5 = 5,
    ActionCustomFnKey_6 = 6,
    ActionCustomFnKey_7 = 7
};

enum ActionFnKeys
{
    ActionFnKey_F1 = 1,
    ActionFnKey_F2 = 2,
    ActionFnKey_F3 = 3,
    ActionFnKey_F4 = 4,
    ActionFnKey_F5 = 5,
    ActionFnKey_F6 = 6,
    ActionFnKey_F7 = 7,
    ActionFnKey_F8 = 8,
    ActionFnKey_F9 = 9,
    ActionFnKey_F10 = 10,
    ActionFnKey_F11 = 11,
    ActionFnKey_F12 = 12,
    ActionFnKey_F13 = 13,
    ActionFnKey_F14 = 14,
    ActionFnKey_F15 = 15,
    ActionFnKey_F16 = 16,
    ActionFnKey_F17 = 17,
    ActionFnKey_F18 = 18,
    ActionFnKey_F19 = 19,
    ActionFnKey_F20 = 20,
    ActionFnKey_F21 = 21,
    ActionFnKey_F22 = 22,
    ActionFnKey_F23 = 23,
    ActionFnKey_F24 = 24
};

enum ActionTabArrowKeys
{
    ActionTabArrowKey_Up = 1,
    ActionTabArrowKey_Down = 2,
    ActionTabArrowKey_Left = 3,
    ActionTabArrowKey_Right = 4,
    ActionTabArrowKey_Backspace = 5,
    ActionTabArrowKey_Tab = 6,
    ActionTabArrowKey_Enter = 7,
    ActionTabArrowKey_PageUp = 8,
    ActionTabArrowKey_PageDown = 9,
    ActionTabArrowKey_Delete = 10,
    ActionTabArrowKey_PrtSc = 11,
    ActionTabArrowKey_Esc = 12,
    ActionTabArrowKey_Home = 13,
    ActionTabArrowKey_End = 14
};

enum ActionMediaKeys
{
    ActionMediaKey_Mute = 1,
    ActionMediaKey_VolumeDown = 2,
    ActionMediaKey_VolumeUp = 3,
    ActionMediaKey_PlayPause = 4,
    ActionMediaKey_Stop = 5,
    ActionMediaKey_NextTrack = 6,
    ActionMediaKey_PreviousTrack = 7,
    ActionMediaKey_WWWHome = 8,
    ActionMediaKey_LocalMachineBrowser = 9,
    ActionMediaKey_Calculator = 10,
    ActionMediaKey_WWWBookmarks = 11,
    ActionMediaKey_WWWSearch = 12,
    ActionMediaKey_WWWStop = 13,
    ActionMediaKey_WWWBack = 14,
    ActionMediaKey_ConsumerControlConfiguration = 15,
    ActionMediaKey_EmailReader = 16

};
