andrewfernie/CADDeck/src/DrawHelper.cpp

#include "DrawHelper.h"

#ifdef READ_EXTERNAL_BATTERY
extern float readExternalBattery();
extern float externalBatteryVoltage;
#endif

char topStatusBarTextLeft[20];
char topStatusBarTextCenter[20];
char topStatusBarTextRight[20];
char bottomStatusBarTextLeft[20];
char bottomStatusBarTextCenter[20];
char bottomStatusBarTextRight[20];

/**
 * @brief This function draws the a "latched" dot. it uses the logonumber, colomn and row to
 *        determine where.
 *
 * @param b int
 * @param col int
 * @param row int
 *
 * @return none
 *
 * @note none
 */
void drawlatched(int b, uint8_t col, uint8_t row)
{
    int offset;
    if (SCREEN_WIDTH < 480) {
        offset = 2;
    }
    else {
        offset = 12;
    }
    int16_t x = KEY_X - KEY_X / 2 + 3 + col * (KEY_W + KEY_SPACING_X);
    int16_t y = KEY_Y - KEY_Y / 2 + 3 + row * (KEY_H + KEY_SPACING_Y);

    tft.fillRoundRect(x - offset, y - offset, 18, 18, 4, generalconfig.latchedColour);
}

/**
* @brief This function draws the logos according to the page
         we are currently on. The pagenumber is a global variable
         and doesn't need to be passed.
*
* @param col int
* @param row int
* @param transparent boolean
* @param latch boolean
*
* @return none
*
* @note row and col start at the top left and are 0 indexed.
*/
void drawlogo(uint8_t col, uint8_t row, bool transparent, bool latch)
{
    //    int16_t x = KEY_X - KEY_X / 2 + 4 + col * (KEY_W + KEY_SPACING_X);
    //    int16_t y = KEY_Y - KEY_Y / 2 + 4 + row * (KEY_H + KEY_SPACING_Y);
    int16_t x = KEY_X + col * (KEY_W + KEY_SPACING_X) - LOGO_SIZE_X_Y / 2;
    int16_t y = KEY_Y + row * (KEY_H + KEY_SPACING_Y) - LOGO_SIZE_X_Y / 2;

    if ((pageNum >= 0) && (pageNum < NUM_PAGES)) {
        if (latch) {
            if (menu[pageNum].button[row][col].pLatchImage == nullptr || !psramAvailable) {
                drawBmp(menu[pageNum].button[row][col].latchlogo, x, y, transparent);
            }
            else {
                drawLogoFromPSRAM(menu[pageNum].button[row][col].pLatchImage, x, y, transparent);
            }
        }
        else {
            if (menu[pageNum].button[row][col].pImage == nullptr || !psramAvailable) {
                drawBmp(menu[pageNum].button[row][col].logo, x, y, transparent);
            }
            else {
                drawLogoFromPSRAM(menu[pageNum].button[row][col].pImage, x, y, transparent);
            }
        }
    }
}

/**
* @brief This function checks if the button is active or inactive.
         Inactive means that the logo is "blank.bmp" and that there are no actions
         defined for the button.
*
* @param page int
* @param col int
* @param row int
*
* @return boolean true if active, false if inactive
*
* @note row and col start at the top left and are 0 indexed.
*/
bool isActiveButton(uint8_t page, uint8_t row, uint8_t col)
{
    bool activeButton = false;
    char logoPathAndName[64];

    strcpy(logoPathAndName, logopath);
    strcat(logoPathAndName, "blank.bmp");

    if (strcmp(menu[pageNum].button[row][col].logo, logoPathAndName) != 0) {
        activeButton = true;
    }
    else {
        if ((menu[pageNum].button[row][col].actions[0].action != ActionEnum::Action_NoAction) ||
            (menu[pageNum].button[row][col].actions[1].action != ActionEnum::Action_NoAction) ||
            (menu[pageNum].button[row][col].actions[2].action != ActionEnum::Action_NoAction))
            activeButton = true;
    }

    return activeButton;
}

/**
 * @brief This function draws a button, both the logo and the surround box.
 *
 * @param page int
 * @param col int
 * @param row int
 *
 * @return none
 *
 * @note row and col start at the top left and are 0 indexed.
 */
void drawButtonRowCol(uint8_t page, uint8_t row, uint8_t col)
{
    bool drawTransparent;
    uint16_t imageBGColor;
    uint16_t buttonBG = TFT_BLACK;
    uint16_t outlineColor = TFT_BLACK;
    bool activeButton = false;

    buttonBG = TFT_BLACK;
    outlineColor = TFT_BLACK;
    activeButton = false;

    uint8_t status = ReturnSuccess;
    activeButton = isActiveButton(pageNum, row, col);

    if (activeButton) {
        if (menu[pageNum].button[row][col].islatched) {
            if (menu[pageNum].button[row][col].pLatchImage == nullptr) {
                if (psramAvailable) {
                    status = loadBmpToPSRAM(menu[pageNum].button[row][col].latchlogo, &(menu[pageNum].button[row][col].pLatchImage));
                    if (status == ReturnSuccess) {
                        imageBGColor = menu[pageNum].button[row][col].pLatchImage[2];
                        menu[pageNum].button[row][col].latchImageBGColour = imageBGColor;
                        menu[pageNum].button[row][col].latchImageBGColourValid = true;
                    }
                    else {
                        MSG_ERROR1("Error allocating PSRAM for latch logo: ", menu[pageNum].button[row][col].latchlogo);
                    }
                }
                else {
                    imageBGColor = getLatchImageBG(pageNum, row, col);
                    menu[pageNum].button[row][col].latchImageBGColour = imageBGColor;
                    menu[pageNum].button[row][col].latchImageBGColourValid = true;
                }
            }
            else {
                imageBGColor = menu[pageNum].button[row][col].latchImageBGColour;
            }
        }
        else {
            if (menu[pageNum].button[row][col].pImage == nullptr) {
                if (psramAvailable) {
                    status = loadBmpToPSRAM(menu[pageNum].button[row][col].logo, &(menu[pageNum].button[row][col].pImage));
                    if (status == ReturnSuccess) {
                        imageBGColor = menu[pageNum].button[row][col].pImage[2];
                        menu[pageNum].button[row][col].imageBGColour = imageBGColor;
                        menu[pageNum].button[row][col].imageBGColourValid = true;
                    }
                    else {
                        MSG_ERROR1("Error allocating PSRAM for logo: ", menu[pageNum].button[row][col].logo);
                    }
                }
                else {
                    imageBGColor = getImageBG(pageNum, row, col);
                    menu[pageNum].button[row][col].imageBGColour = imageBGColor;
                    menu[pageNum].button[row][col].imageBGColourValid = true;
                }
            }
            else {
                imageBGColor = menu[pageNum].button[row][col].imageBGColour;
            }
        }

        if (imageBGColor > 0) {
            buttonBG = imageBGColor;
            drawTransparent = false;
        }
        else {
            if (menu[pageNum].button[row][col].actions[0].action == Action_ChangePage) {
                buttonBG = generalconfig.menuButtonColour;
                drawTransparent = true;
            }
            else {
                buttonBG = generalconfig.functionButtonColour;
                drawTransparent = true;
            }
        }
        outlineColor = TFT_WHITE;
    }
    tft.setFreeFont(LABEL_FONT);
    key[row][col].initButton(&tft, KEY_X + col * (KEY_W + KEY_SPACING_X),
                             KEY_Y + row * (KEY_H + KEY_SPACING_Y),  // x, y, w, h, outline, fill, text
                             KEY_W, KEY_H, outlineColor, buttonBG, outlineColor,
                             (char *)"", KEY_TEXTSIZE);
    key[row][col].drawButton();
    // After drawing the button outline we call this to draw a logo.
    if (activeButton) {
        drawlogo(col, row, drawTransparent, menu[pageNum].button[row][col].islatched);
    }
}

/**
* @brief This function draws the set buttons that are on each page.
         Pagenumber is global and doesn't need to be passed.
*
* @param none
*
* @return none
*
* @note none
*/
void drawKeypad()
{
    if ((pageNum >= 0) && (pageNum < NUM_PAGES)) {
        // Draw the button outlines and fill them with colours
        for (uint8_t row = 0; row < BUTTON_ROWS; row++) {
            for (uint8_t col = 0; col < BUTTON_COLS; col++) {
                drawButtonRowCol(pageNum, row, col);
            }
        }

        drawTopStatusBar(true);     // Draw the top status bar, with a forced redraw
        drawBottomStatusBar(true);  // Draw the bottom status bar, with a forced redraw
    }

    else if (pageNum == SPECIAL_4_PAGE) {
        // Pagenum max + 4 means that a JSON config failed to load completely.
        tft.fillScreen(TFT_BLACK);
        tft.setCursor(KEY_MARGIN_X, KEY_MARGIN_Y_TOP);
        tft.setTextFont(2);
        tft.setTextSize(1);
        tft.setTextColor(TFT_WHITE, TFT_BLACK);

        tft.printf("  %s failed to load and might be corrupted.\n", jsonFileFail);
        tft.println("  You can reset that specific file to default by opening the serial monitor");
        tft.printf("  and typing \"reset %s\"\n", jsonFileFail);
        tft.println("  If you don't do this, the configurator will fail to load.");
    }
}

/* ------------- Print an error message the TFT screen  ----------------
Purpose: This function prints an message to the TFT screen on a black
         background.
Input  : String message
Output : none
Note   : none
*/

void drawErrorMessage(String message)
{
    tft.fillScreen(TFT_BLACK);
    tft.setCursor(KEY_MARGIN_X, KEY_MARGIN_Y_TOP);
    tft.setTextFont(2);
    tft.setTextSize(1);
    tft.setTextColor(TFT_WHITE, TFT_BLACK);
    tft.println(message);
}

/**
* @brief This function gets the Bluetooth device address and prints it to the serial monitor
         and the TFT screen in a 6 byte format, seperating each byte by ":".
*
* @param none
*
* @return none
*
* @note e.g. 00:11:22:33:22:EE
*/
void printDeviceAddress()
{
    const uint8_t *point = esp_bt_dev_get_address();

    for (int i = 0; i < 6; i++) {
        char str[3];

        sprintf(str, "%02X", (int)point[i]);
        // Serial.print(str);
        tft.print(str);

        if (i < 5) {
            // Serial.print(":");
            tft.print(":");
        }
    }
}

/**
* @brief This function prints some information about the current version
         and setup of CADDeck to the TFT screen.
*
* @param none
*
* @return none
*
* @note none
*/
void printinfo()
{
    tft.fillScreen(TFT_BLACK);
    tft.setCursor(KEY_MARGIN_X, KEY_MARGIN_Y_TOP);
    tft.setTextFont(2);
    if (SCREEN_WIDTH < 480) {
        tft.setTextSize(1);
    }
    else {
        tft.setTextSize(1);
    }
    tft.setTextColor(TFT_WHITE, TFT_BLACK);
    tft.printf("Version: %s\n", versionnumber);

#ifdef TOUCH_INTERRUPT_PIN
    if (generalconfig.sleepenable) {
        tft.println("Sleep: Enabled");
        tft.printf("Sleep timer: %u minutes\n", generalconfig.sleeptimer);
    }
    else {
        tft.println("Sleep: Disabled");
    }
#else
    tft.println("Sleep: Disabled");
#endif

    if (generalconfig.usbcommsenable) {
        tft.println("USB Comms: Enabled");
    }
    else {
        tft.println("USB Comms: Disabled");
    }

    if (cadconfig.spacemouse_enable) {
        tft.println("Spacemouse Mode: Enabled");
    }
    else {
        tft.println("Spacemouse Mode: Disabled");
    }

#ifdef speakerPin
    if (generalconfig.beep) {
        tft.println("Speaker: Enabled");
    }
    else {
        tft.println("Speaker: Disabled");
    }
#else
    tft.println("Speaker: Disabled");
#endif

#ifdef READ_EXTERNAL_BATTERY
    tft.printf("Battery voltage: %f V\n", externalBatteryVoltage);
#endif

    tft.print("Filesystem storage. Total: ");
    tft.print(FILESYSTEM.totalBytes() / 1000);
    tft.print(" kB, used: ");
    tft.print(FILESYSTEM.usedBytes() / 1000);
    tft.print(" kB, free: ");
    long freemem = FILESYSTEM.totalBytes() - FILESYSTEM.usedBytes();
    tft.print(freemem / 1000);
    tft.println(" kB");
    // tft.print("BLE Keyboard version: ");
    // tft.println(BLE_COMBO_VERSION);
    tft.print("ArduinoJson version: ");
    tft.println(ARDUINOJSON_VERSION);
    tft.print("TFT_eSPI version: ");
    tft.println(TFT_ESPI_VERSION);
    tft.print("ESP-IDF: ");
    tft.println(esp_get_idf_version());
    tft.println(esp_get_idf_version());
    tft.print("Free heap: ");
    float freeram = esp_get_free_heap_size();
    tft.print(freeram / 1000);
    tft.print("kB, Minimum free heap: ");
    freeram = esp_get_minimum_free_heap_size();
    tft.print(freeram / 1000);
    tft.println("kB");
    if (psramAvailable) {
        tft.print("Used PSRAM: ");
        long kBPSRAM = usedPSRAM();
        tft.print(kBPSRAM / 1000);
        tft.print("kB, ");
        tft.print("Free PSRAM: ");
        kBPSRAM = ESP.getFreePsram();
        tft.print(kBPSRAM / 1000);
        tft.print("kB");
    }
    else {
        tft.println("PSRAM: Not available");
    }
    displayinginfo = true;
}

/**
 * @brief This function displays the description for each of the H/W buttons to the TFT screen.
 *
 * @param none
 *
 * @return none
 *
 * @note none
 */
void printButtonInfo(uint8_t program)
{
    tft.fillScreen(TFT_BLACK);
    tft.setCursor(KEY_MARGIN_X, KEY_MARGIN_Y_TOP);
    tft.setTextFont(2);
    if (SCREEN_WIDTH < 480) {
        tft.setTextSize(1);
    }
    else {
        tft.setTextSize(1);
    }
    tft.setTextColor(TFT_WHITE, TFT_BLACK);
    tft.printf("CAD Program: %s\n", cadprogramconfig[cadconfig.current_program].name);

    for (int i = 0; i < NUM_HW_BUTTONS; i++) {
        tft.printf("  Button %d: %s\n", i, cadprogramconfig[cadconfig.current_program].hw_button_descriptions[i]);
    }

    displayingButtonDescriptions = true;
}

uint32_t usedPSRAM()
{
    return ESP.getPsramSize() - ESP.getFreePsram();
}

/**
 * @brief This function displays the value of some IO values on the TFT screen.
 *
 * @param none
 *
 * @return none
 *
 * @note none
 */
void printIOValues()
{
    if (!displayingIOValues) {
        tft.fillScreen(TFT_BLACK);
    }

    tft.setCursor(KEY_MARGIN_X, KEY_MARGIN_Y_TOP);
    tft.setTextFont(2);
    if (SCREEN_WIDTH < 480) {
        tft.setTextSize(1);
    }
    else {
        tft.setTextSize(1);
    }
    tft.setTextColor(TFT_WHITE, TFT_BLACK);
    tft.printf("Version: %s       \n", versionnumber);

    tft.printf("Joystick X: %d,  %f     \n", joystick.RawX(), joystick.x());
    tft.printf("Joystick Y: %d,  %f     \n", joystick.RawY(), joystick.y());

    tft.printf("Zoom: %d,  %f     \n", zoomControl.RawValue(), zoomControl.Value());
    tft.printf("Rotate: %d,  %f     \n", rotateControl.RawValue(), rotateControl.Value());

    //    PCF857X::DigitalInput di = pcf857X.digitalReadAll();
    tft.print(" Button 0: ");
    tft.println(get_pcf857X_bit(pcf857X_inputs, BUTTON_0));

    tft.print(" Buttons 1-2-3-4-5: ");
    tft.print(get_pcf857X_bit(pcf857X_inputs, BUTTON_1));
    tft.print(" - ");
    tft.print(get_pcf857X_bit(pcf857X_inputs, BUTTON_2));
    tft.print(" - ");
    tft.print(get_pcf857X_bit(pcf857X_inputs, BUTTON_3));
    tft.print(" - ");
    tft.print(get_pcf857X_bit(pcf857X_inputs, BUTTON_4));
    tft.print(" - ");
    tft.println(get_pcf857X_bit(pcf857X_inputs, BUTTON_5));

    tft.print(" Buttons 6-7-8-9-10: ");
    tft.print(get_pcf857X_bit(pcf857X_inputs, BUTTON_6));
    tft.print(" - ");
    tft.print(get_pcf857X_bit(pcf857X_inputs, BUTTON_7));
    tft.print(" - ");
    tft.print(get_pcf857X_bit(pcf857X_inputs, BUTTON_8));
    tft.print(" - ");
    tft.print(get_pcf857X_bit(pcf857X_inputs, BUTTON_9));
    tft.print(" - ");
    tft.println(get_pcf857X_bit(pcf857X_inputs, BUTTON_10));

    delay(100);

    displayingIOValues = true;
}

/**
 * @brief This function displays some basic status information at the top of the screen.
 *
 * @param force_redraw bool. If true, the status bar will be redrawn even if the text is the same.
 *
 * @return none
 *
 * @note none
 */
void drawTopStatusBar(bool force_redraw = true)
{
    char buffer[20];
    int comparison;

    if (Keyboard.isConnected()) {
        snprintf(buffer, sizeof(buffer), "BT OK - %s", cadprogramconfig[cadconfig.current_program].name);
    }
    else {
        snprintf(buffer, sizeof(buffer), "No BT - %s", cadprogramconfig[cadconfig.current_program].name);
    }
    comparison = strncmp(buffer, topStatusBarTextLeft, sizeof(buffer));
    if (comparison != 0 || force_redraw) {
        tft.fillRect(0, 0, SCREEN_WIDTH / 3, KEY_MARGIN_Y_TOP, TFT_BLACK);
        tft.setCursor(KEY_MARGIN_X, 3);
        tft.setTextFont(2);
        tft.setTextSize(1);
        tft.setTextColor(TFT_WHITE, TFT_BLACK);
        tft.print(buffer);

        strncpy(topStatusBarTextLeft, buffer, sizeof(topStatusBarTextLeft));
    }

    strncpy(buffer, menu[pageNum].name, sizeof(buffer));
    comparison = strncmp(buffer, topStatusBarTextCenter, sizeof(buffer));

    if (comparison != 0 || force_redraw) {
        tft.fillRect(SCREEN_WIDTH / 3, 0, SCREEN_WIDTH / 3, KEY_MARGIN_Y_TOP, TFT_BLACK);
        tft.setTextFont(2);
        tft.setTextSize(2);
        tft.setCursor(SCREEN_WIDTH / 2 - tft.textWidth(buffer, 2) / 2, 0);
        tft.setTextColor(TFT_WHITE, TFT_BLACK);
        tft.print(buffer);

        strncpy(topStatusBarTextCenter, buffer, sizeof(topStatusBarTextCenter));
    }

#ifdef READ_EXTERNAL_BATTERY
    snprintf(buffer, sizeof(buffer), "%4.1fV\n", externalBatteryVoltage);
    int x_start = SCREEN_WIDTH - KEY_MARGIN_X - tft.textWidth(buffer, 2);
    comparison = strncmp(buffer, topStatusBarTextRight, sizeof(buffer));

    if (comparison != 0 || force_redraw) {
        tft.fillRect(SCREEN_WIDTH - SCREEN_WIDTH / 3, 0, SCREEN_WIDTH / 3, KEY_MARGIN_Y_TOP, TFT_BLACK);
        tft.setCursor(x_start, 3);
        tft.setTextFont(2);
        tft.setTextSize(1);
        tft.setTextColor(TFT_WHITE, TFT_BLACK);
        tft.print(buffer);

        strncpy(topStatusBarTextRight, buffer, sizeof(topStatusBarTextRight));
    }
#endif
}

/**
 * @brief This function displays some basic status information at the bottom of the screen.
 *
 * @param force_redraw bool. If true, the status bar will be redrawn even if the text is the same.
 *
 * @return none
 *
 * @note  It is not currently being used, but is provided for potential future use.
 */
void drawBottomStatusBar(bool force_redraw = true)
{
    char buffer[20];
    int comparison;

    strncpy(buffer, "", sizeof(buffer));
    comparison = strncmp(buffer, bottomStatusBarTextLeft, sizeof(buffer));
    if (comparison != 0 || force_redraw) {
        tft.fillRect(0, SCREEN_HEIGHT - KEY_MARGIN_Y_BOTTOM, SCREEN_WIDTH / 3, KEY_MARGIN_Y_BOTTOM, TFT_BLACK);
        tft.setCursor(KEY_MARGIN_X, SCREEN_HEIGHT - KEY_MARGIN_Y_BOTTOM);
        tft.setTextFont(2);
        tft.setTextSize(1);
        tft.setTextColor(TFT_WHITE, TFT_BLACK);
        tft.print(buffer);

        strncpy(bottomStatusBarTextLeft, buffer, sizeof(bottomStatusBarTextLeft));
    }

    strncpy(buffer, "", sizeof(buffer));
    comparison = strncmp(buffer, bottomStatusBarTextCenter, sizeof(buffer));

    if (comparison != 0 || force_redraw) {
        tft.fillRect(SCREEN_WIDTH / 3, SCREEN_HEIGHT - KEY_MARGIN_Y_BOTTOM, SCREEN_WIDTH / 3, KEY_MARGIN_Y_BOTTOM, TFT_BLACK);
        tft.setCursor(SCREEN_WIDTH / 3 + KEY_MARGIN_X, SCREEN_HEIGHT - KEY_MARGIN_Y_BOTTOM);
        tft.setTextFont(2);
        tft.setTextSize(1);
        tft.setTextColor(TFT_WHITE, TFT_BLACK);
        tft.print(buffer);

        strncpy(bottomStatusBarTextCenter, buffer, sizeof(bottomStatusBarTextCenter));
    }

    strncpy(buffer, "", sizeof(buffer));
    comparison = strncmp(buffer, bottomStatusBarTextRight, sizeof(bottomStatusBarTextRight));

    if (comparison != 0 || force_redraw) {
        tft.fillRect(SCREEN_WIDTH - SCREEN_WIDTH / 3, SCREEN_HEIGHT - KEY_MARGIN_Y_BOTTOM, SCREEN_WIDTH / 3, KEY_MARGIN_Y_BOTTOM, TFT_BLACK);
        tft.setCursor(SCREEN_WIDTH - SCREEN_WIDTH / 3, SCREEN_HEIGHT - KEY_MARGIN_Y_BOTTOM);
        tft.setTextFont(2);
        tft.setTextSize(1);
        tft.setTextColor(TFT_WHITE, TFT_BLACK);
        tft.print(buffer);

        strncpy(bottomStatusBarTextRight, buffer, sizeof(bottomStatusBarTextRight));
    }
}

/**
 * @brief This function validates a page number 
 *
 * @param page uint8_t. The page number to be validated
 *
 * @return true if the page number is valid, false otherwise
 *
 * @note  It is not currently being used, but is provided for potential future use.
 */
uint8_t isValidPageNumber(uint8_t page)
{
    uint8_t valid = false;

    valid = (page >= 0) && (page <= MAX_PAGE_NUM);

    return valid;
}
