andrewfernie/CADDeck/include/UserActions.h

#pragma once
#include "CADDeck.h"
void printLargeString(const char string[]);
void userAction1();
void userAction2();
void userAction3();
void userAction4();
void userAction5();
void userAction6();
void userAction7();
